DanielKarp/Caltrain-EInk-Bike-Tag/photos/PXL_20260421_231036464.jpg

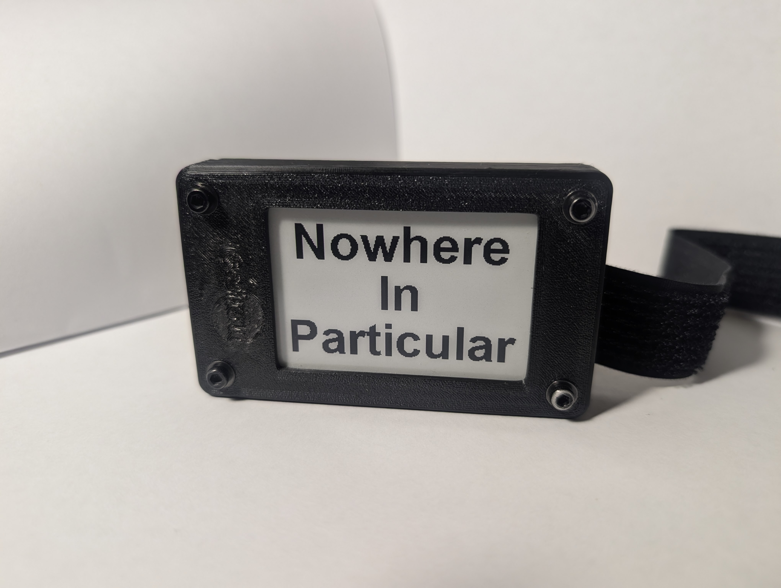
photos/PXL_20260421_231036464.jpg
