DanielKarp/Caltrain-EInk-Bike-Tag/photos/PXL_20260421_231038806.jpg

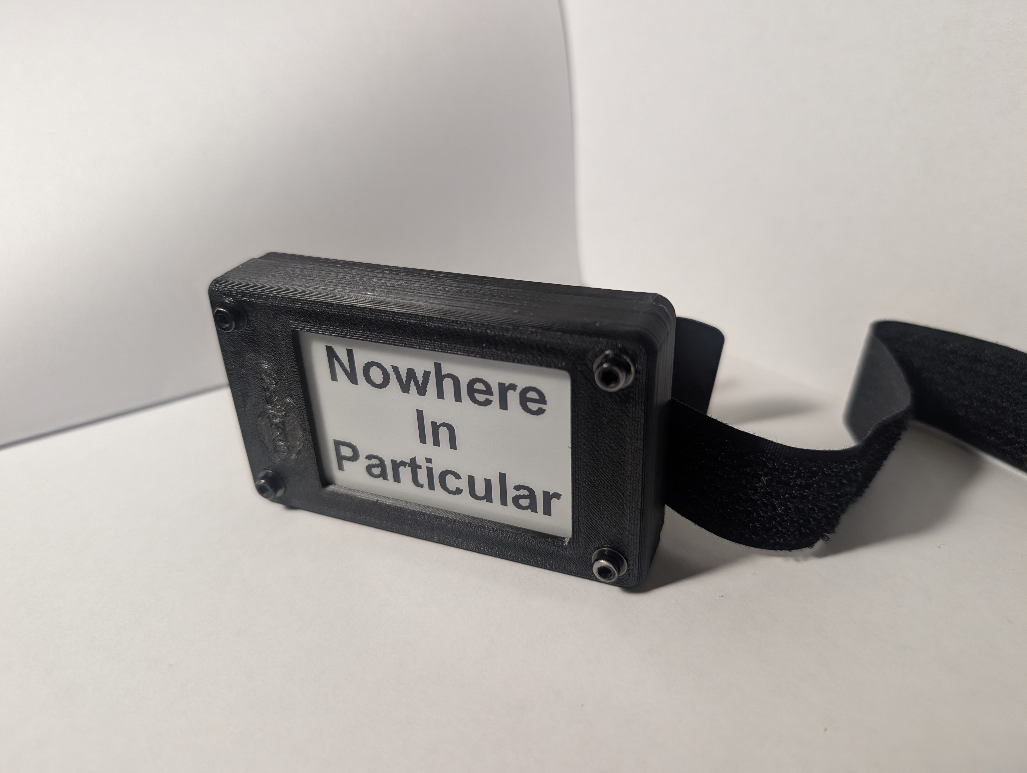
photos/PXL_20260421_231038806.jpg
