DanielKarp/Caltrain-EInk-Bike-Tag/photos/PXL_20260421_231105509.jpg

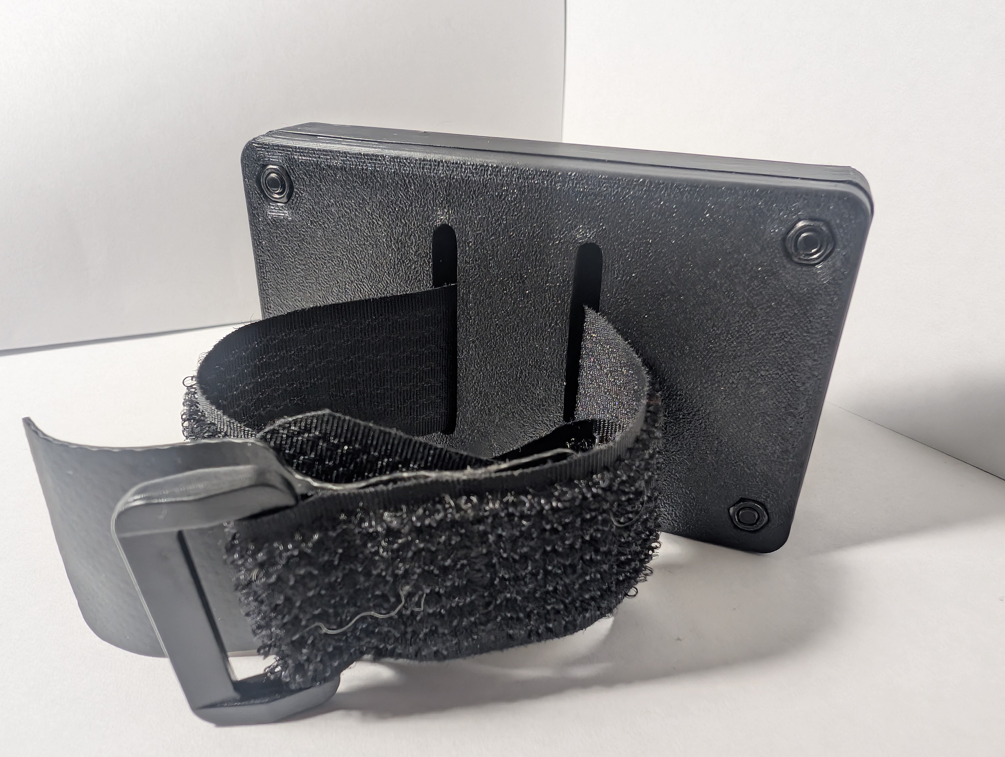
photos/PXL_20260421_231105509.jpg
