DanielKarp/Caltrain-EInk-Bike-Tag/photos/PXL_20260421_231125235.jpg

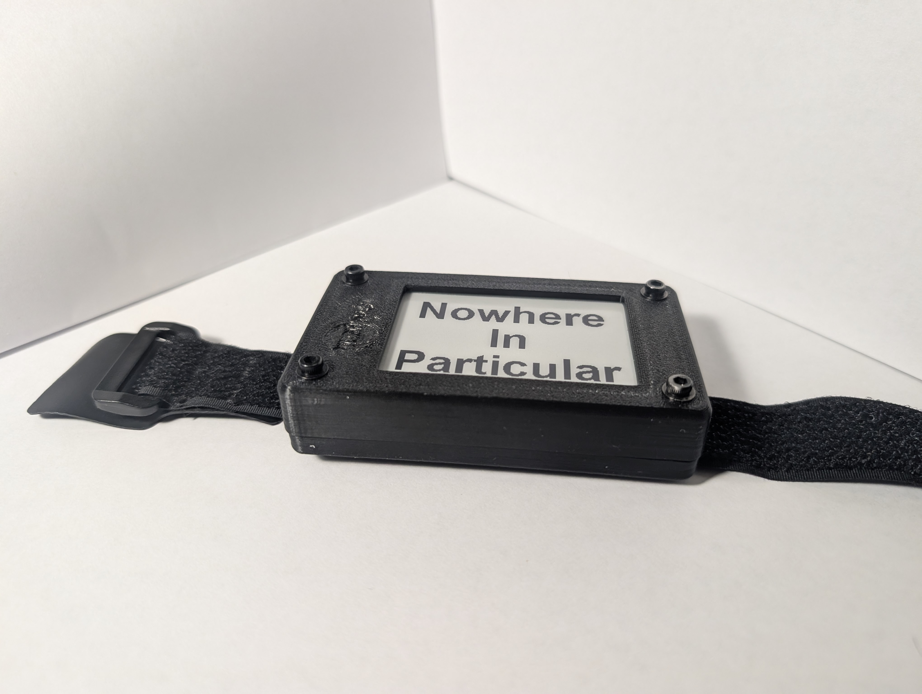
photos/PXL_20260421_231125235.jpg
